florindumitrescu94/DashBoard_PowerBox_V2/DashBoard_PowerBox_V2_Documents/Board_dimensions.jpg

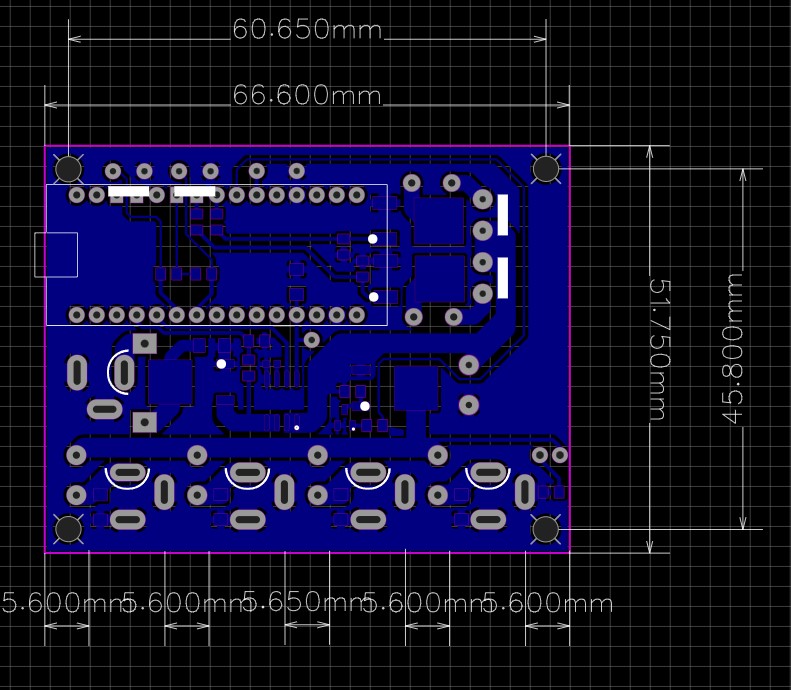
DashBoard_PowerBox_V2_Documents/Board_dimensions.jpg
