florindumitrescu94/DashBoard_PowerBox_V2/DashBoard_PowerBox_V2_Documents/box_3d_model.jpg

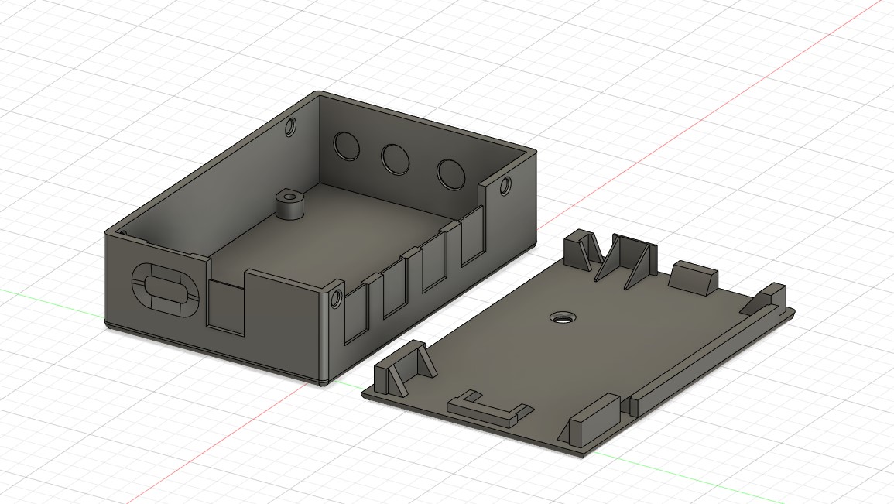
DashBoard_PowerBox_V2_Documents/box_3d_model.jpg
