florindumitrescu94/DashBoard_PowerBox_V2/DashBoard_PowerBox_V2_Documents/dashboard_finished_front.jpg

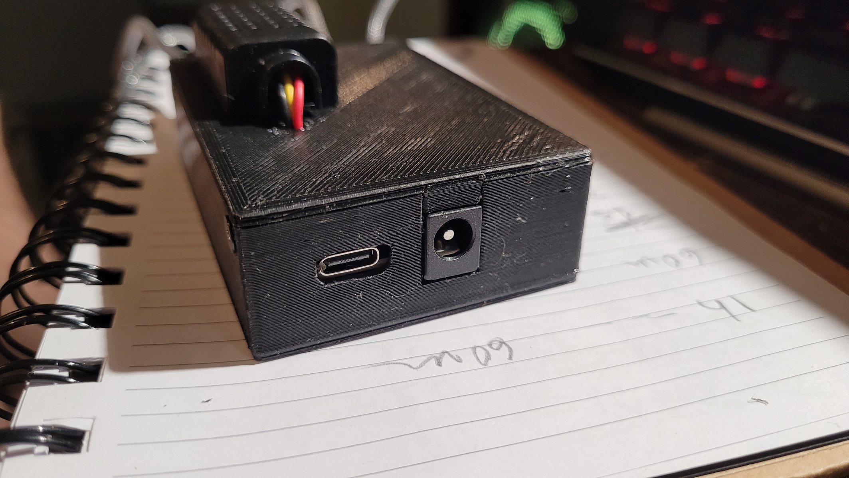
DashBoard_PowerBox_V2_Documents/dashboard_finished_front.jpg
