florindumitrescu94/DashBoard_PowerBox_V2/DashBoard_PowerBox_V2_Documents/pcb_after_etch.jpg

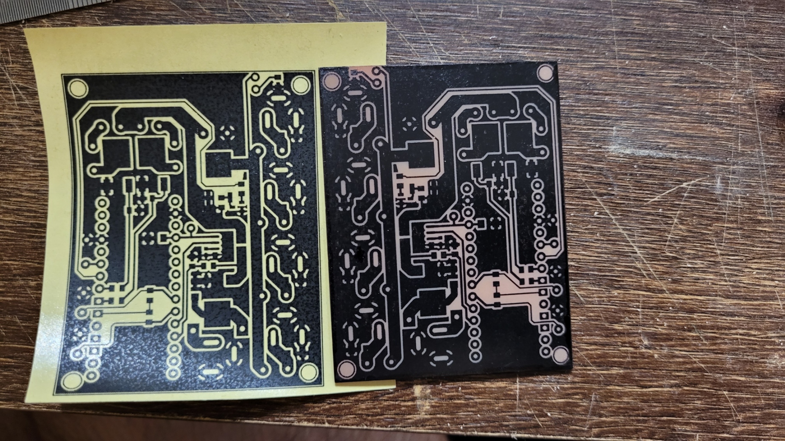
DashBoard_PowerBox_V2_Documents/pcb_after_etch.jpg
