florindumitrescu94/DashBoard_PowerBox_V2/DashBoard_PowerBox_V2_Documents/dashboard_inside_wiring.jpg

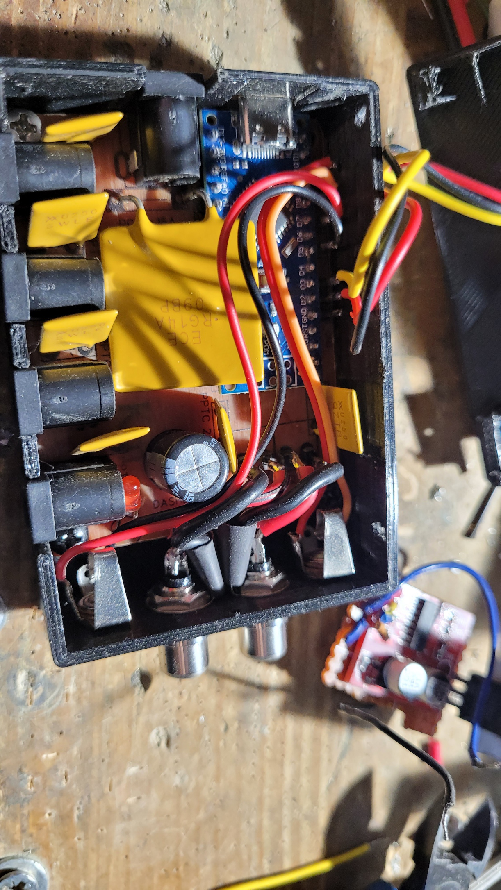
DashBoard_PowerBox_V2_Documents/dashboard_inside_wiring.jpg
